aryasenna/InvenGlove/InvenGlove Connector/Resources/closed.png

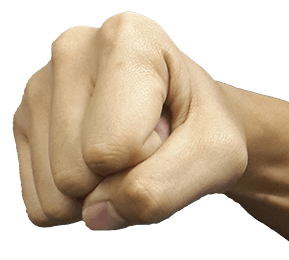
InvenGlove Connector/Resources/closed.png
