aryasenna/InvenGlove/InvenGlove Connector/Resources/down.png

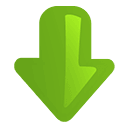
InvenGlove Connector/Resources/down.png
