aryasenna/InvenGlove/InvenGlove Connector/Resources/left.png

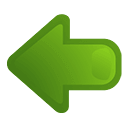
InvenGlove Connector/Resources/left.png
