aryasenna/InvenGlove/InvenGlove Connector/Resources/open.png

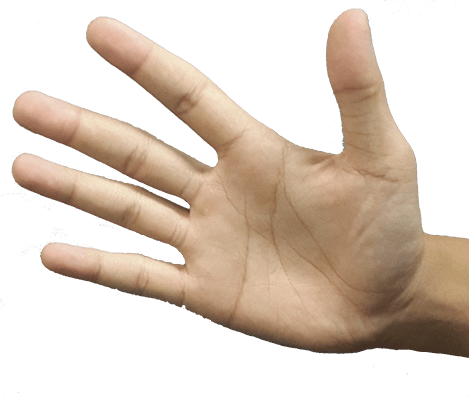
InvenGlove Connector/Resources/open.png
